gipi/pov-project/firmware/bootloaders/CDC/Board/LEDs.h

/*
             LUFA Library
     Copyright (C) Dean Camera, 2013.

  dean [at] fourwalledcubicle [dot] com
           www.lufa-lib.org
*/

/*
  Copyright 2013  Dean Camera (dean [at] fourwalledcubicle [dot] com)

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
  The author disclaims all warranties with regard to this
  software, including all implied warranties of merchantability
  and fitness.  In no event shall the author be liable for any
  special, indirect or consequential damages or any damages
  whatsoever resulting from loss of use, data or profits, whether
  in an action of contract, negligence or other tortious action,
  arising out of or in connection with the use or performance of
  this software.
*/

/** \file
 *  \brief Board specific LED driver header for the Tempusdictum Benito.
 *  \copydetails Group_LEDs_CIAODUINO
 *
 *  \note This file should not be included directly. It is automatically included as needed by the LEDs driver
 *        dispatch header located in LUFA/Drivers/Board/LEDs.h.
 */

/** \ingroup Group_LEDs
 *  \defgroup Group_LEDs_CIADUINO CIAODUINO
 *  \brief Board specific LED driver header for the Ciaoduino board.
 *
 *  <table>
 *    <tr><th>Name</th><th>Color</th><th>Info</th><th>Active Level</th><th>Port Pin</th></tr>
 *    <tr><td>LEDS_LED1</td><td>Green</td><td>TX LED</td><td>Low</td><td>PORTC.7</td></tr>
 *    <tr><td>LEDS_LED2</td><td>Red</td><td>RX LED</td><td>Low</td><td>PORTC.6</td></tr>
 *  </table>
 *
 *  @{
 */

#ifndef __LEDS_CIAODUINO_H__
#define __LEDS_CIAODUINO_H__

	/* Includes: */
		//#include "../../../../Common/Common.h"

	/* Enable C linkage for C++ Compilers: */
		#if defined(__cplusplus)
			extern "C" {
		#endif

	/* Preprocessor Checks: */
		#if !defined(__INCLUDE_FROM_LEDS_H)
			#error Do not include this file directly. Include LUFA/Drivers/Board/LEDS.h instead.
		#endif

	/* Public Interface - May be used in end-application: */
		/* Macros: */
			/** LED mask for the first LED on the board. */
			#define LEDS_LED1        (1 << 7)

			/** LED mask for the second LED on the board. */
			#define LEDS_LED2        (1 << 6)

			/** LED mask for all the LEDs on the board. */
			#define LEDS_ALL_LEDS    (LEDS_LED1 | LEDS_LED2)

			/** LED mask for none of the board LEDs. */
			#define LEDS_NO_LEDS     0

		/* Inline Functions: */
		#if !defined(__DOXYGEN__)
			static inline void LEDs_Init(void)
			{
				DDRC  |= LEDS_ALL_LEDS;
				PORTC |= LEDS_ALL_LEDS;
			}

			static inline void LEDs_Disable(void)
			{
				DDRC  &= ~LEDS_ALL_LEDS;
				PORTC &= ~LEDS_ALL_LEDS;
			}

			static inline void LEDs_TurnOnLEDs(const uint8_t LEDMask)
			{
				PORTC &= ~LEDMask;
			}

			static inline void LEDs_TurnOffLEDs(const uint8_t LEDMask)
			{
				PORTC |= LEDMask;
			}

			static inline void LEDs_SetAllLEDs(const uint8_t LEDMask)
			{
				PORTC = ((PORTC | LEDS_ALL_LEDS) & ~LEDMask);
			}

			static inline void LEDs_ChangeLEDs(const uint8_t LEDMask,
			                                   const uint8_t ActiveMask)
			{
				PORTC = ((PORTC | LEDMask) & ~ActiveMask);
			}

			static inline void LEDs_ToggleLEDs(const uint8_t LEDMask)
			{
				PINC  = LEDMask;
			}

			static inline uint8_t LEDs_GetLEDs(void) ATTR_WARN_UNUSED_RESULT;
			static inline uint8_t LEDs_GetLEDs(void)
			{
				return (~PORTC & LEDS_ALL_LEDS);
			}
		#endif

	/* Disable C linkage for C++ Compilers: */
		#if defined(__cplusplus)
			}
		#endif

#endif

/** @} */
